Circuit-Digest/LiteWing/Documents/Images/Altitude-Change-Litewing.gif

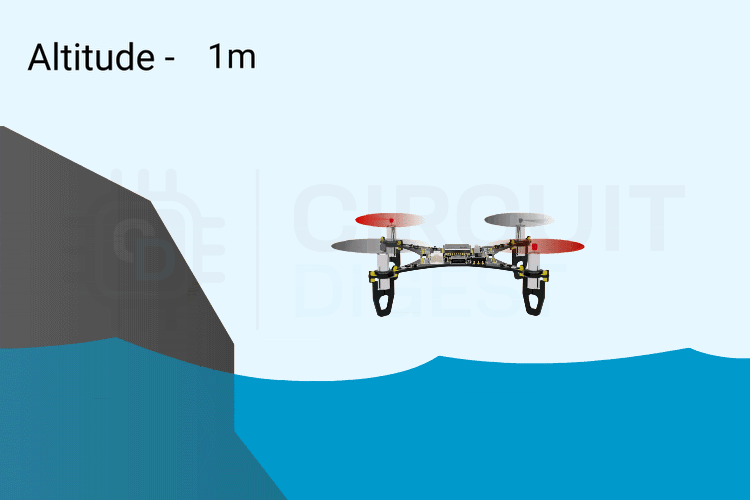
Documents/Images/Altitude-Change-Litewing.gif
