Circuit-Digest/LiteWing/Documents/Images/Calculated-height-displayed-GIF.gif

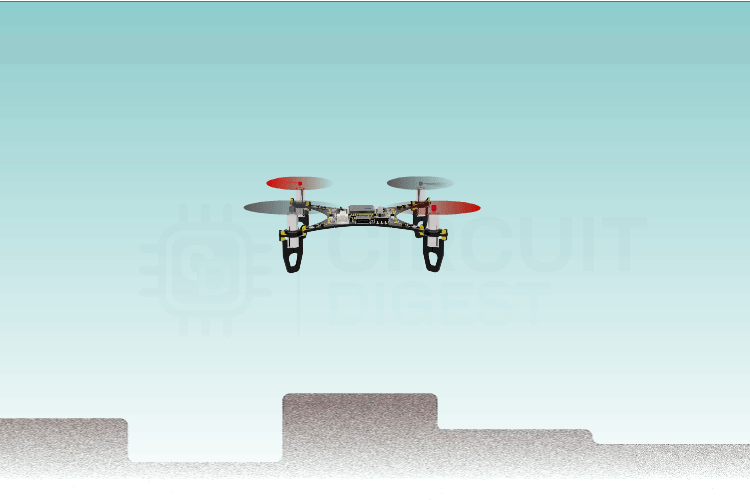
Documents/Images/Calculated-height-displayed-GIF.gif
