Circuit-Digest/LiteWing/Documents/Images/GIF-Ultrasonic-Wave-Height-Hold.gif

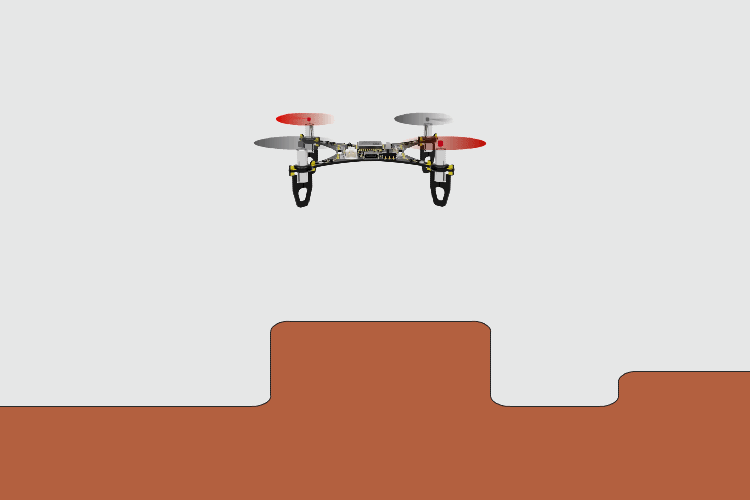
Documents/Images/GIF-Ultrasonic-Wave-Height-Hold.gif
