Circuit-Digest/LiteWing/Python-Scripts/crazyflie-clients-python/docs/images/base_station_geo_dialog.png

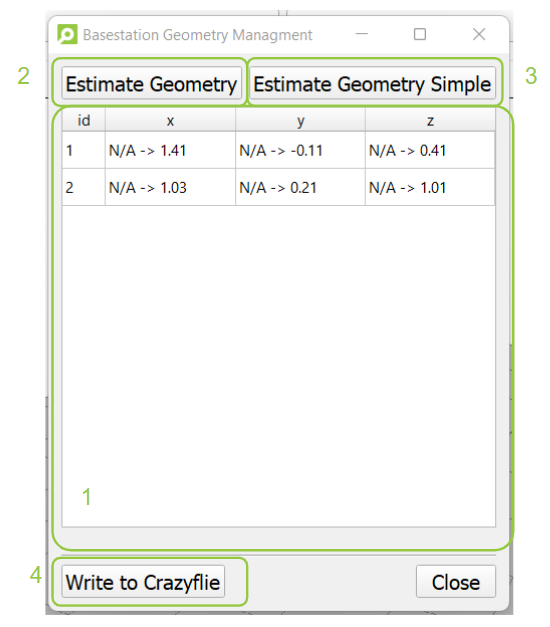
Python-Scripts/crazyflie-clients-python/docs/images/base_station_geo_dialog.png
