Circuit-Digest/LiteWing/Python-Scripts/crazyflie-clients-python/docs/images/bootloader-recovery.png

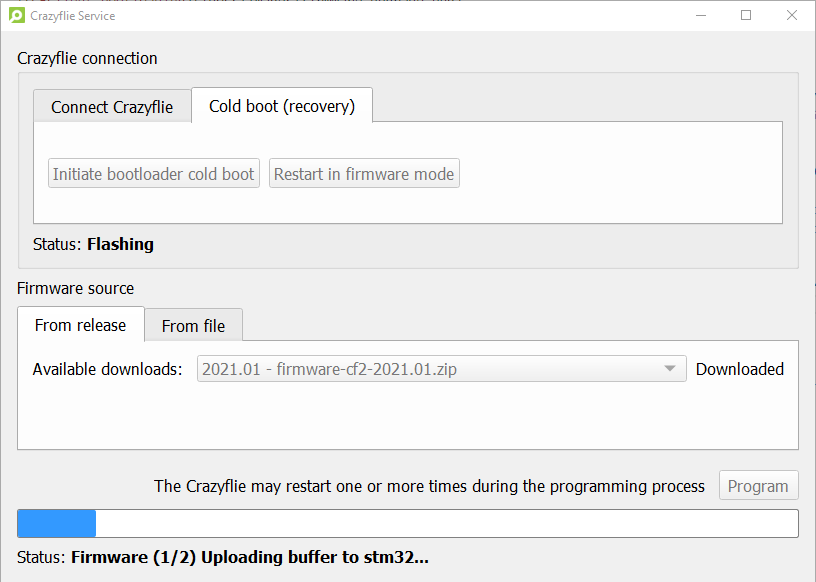
Python-Scripts/crazyflie-clients-python/docs/images/bootloader-recovery.png
