Circuit-Digest/LiteWing/Python-Scripts/crazyflie-clients-python/docs/images/cfclient_anchor_identification.png

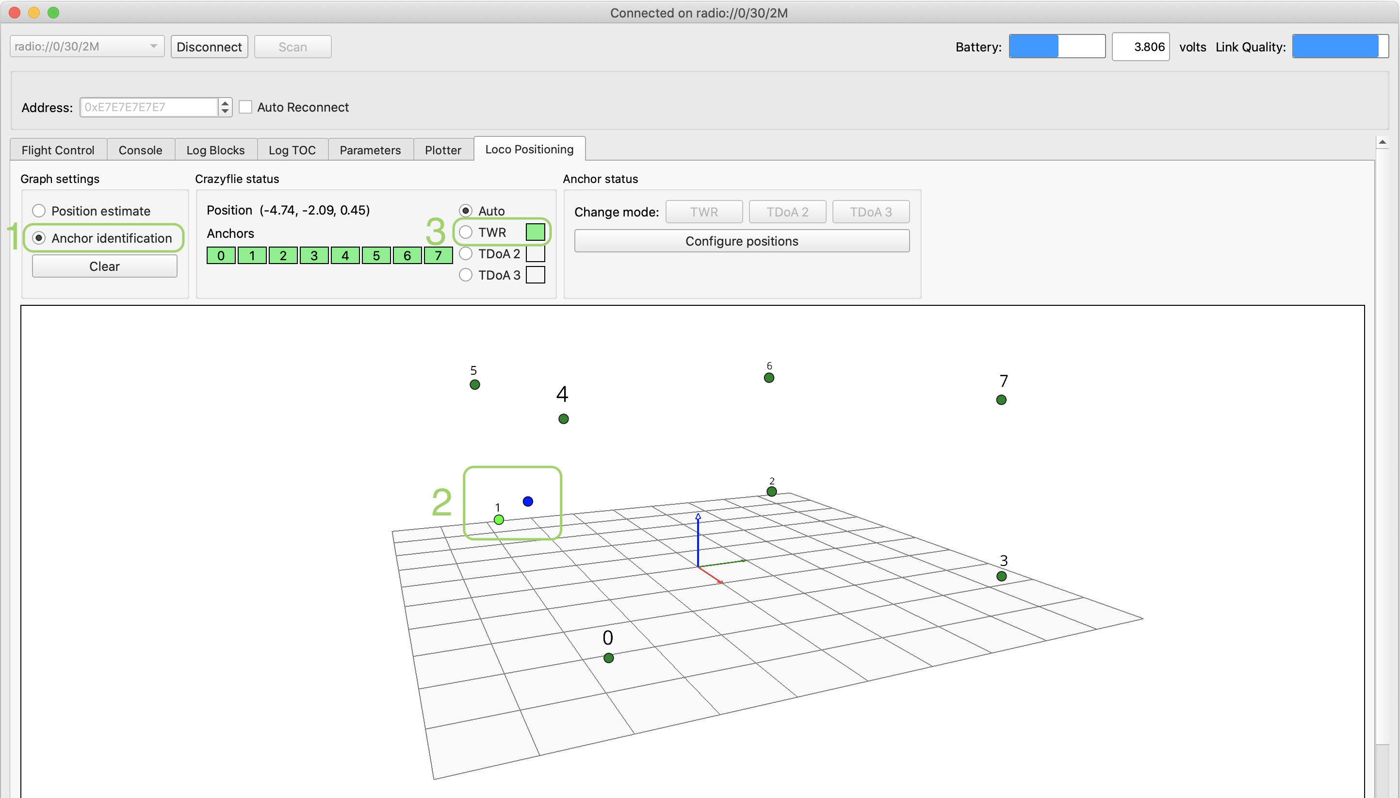
Python-Scripts/crazyflie-clients-python/docs/images/cfclient_anchor_identification.png
