Circuit-Digest/LiteWing/Python-Scripts/crazyflie-clients-python/docs/images/cfclient_connect_dialog.png

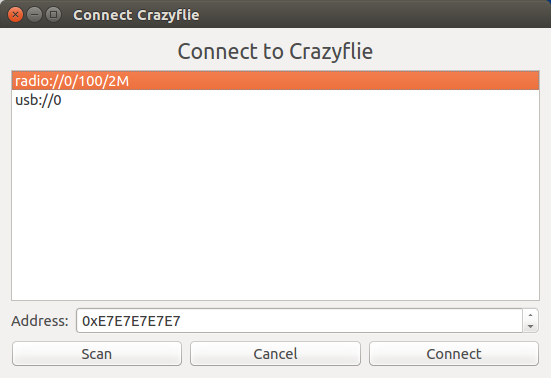
Python-Scripts/crazyflie-clients-python/docs/images/cfclient_connect_dialog.png
