Circuit-Digest/LiteWing/Python-Scripts/crazyflie-clients-python/docs/images/cfclient_connected.png

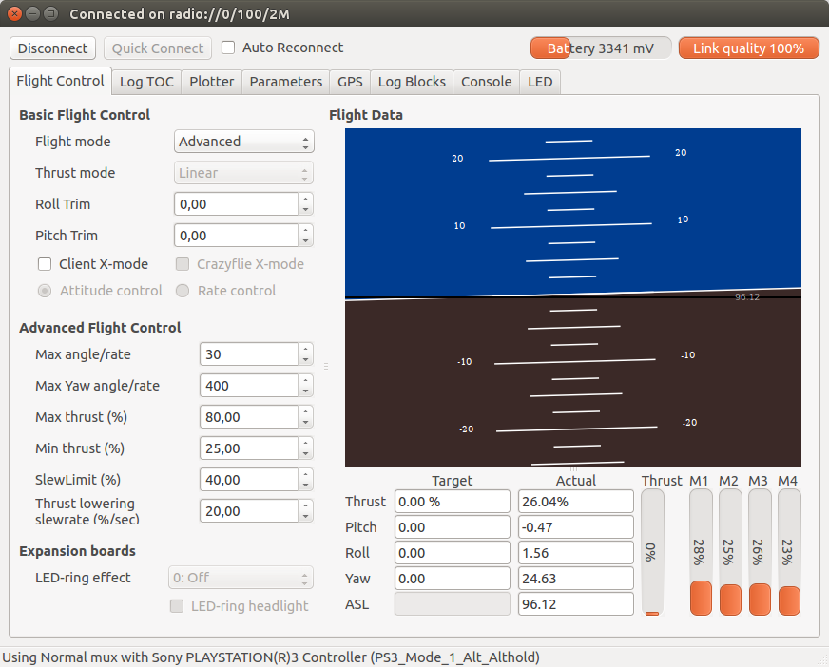
Python-Scripts/crazyflie-clients-python/docs/images/cfclient_connected.png
