Circuit-Digest/LiteWing/Python-Scripts/crazyflie-clients-python/docs/images/cfclient_console_marked.png

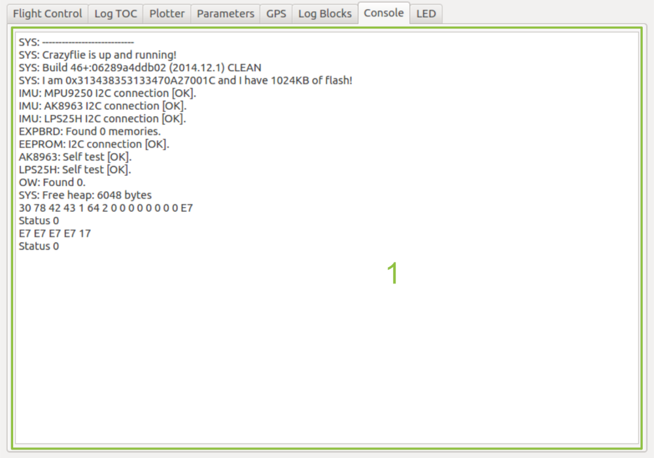
Python-Scripts/crazyflie-clients-python/docs/images/cfclient_console_marked.png
