Circuit-Digest/LiteWing/Python-Scripts/crazyflie-clients-python/docs/images/cfclient_frontpage.png

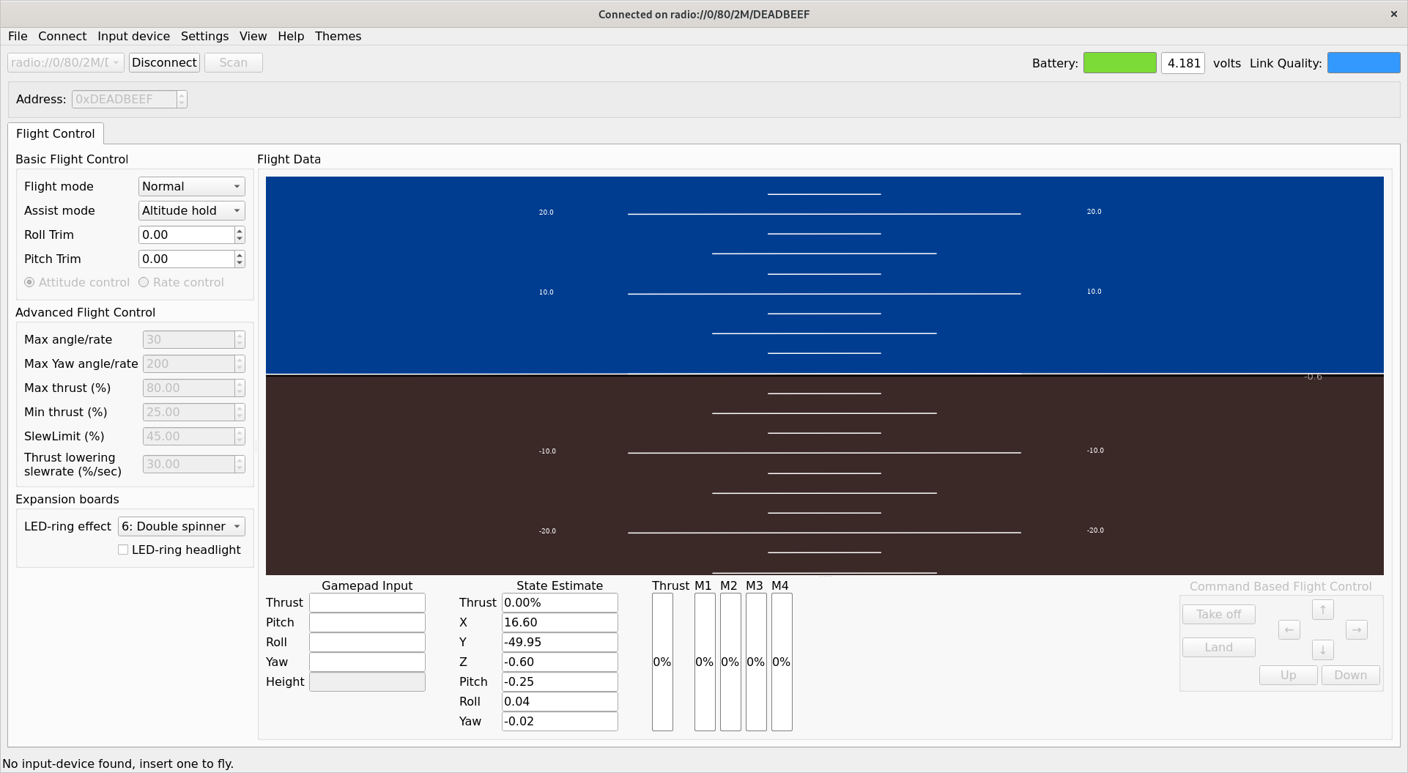
Python-Scripts/crazyflie-clients-python/docs/images/cfclient_frontpage.png
