Circuit-Digest/LiteWing/Python-Scripts/crazyflie-clients-python/docs/images/cfclient_input_student_device.png

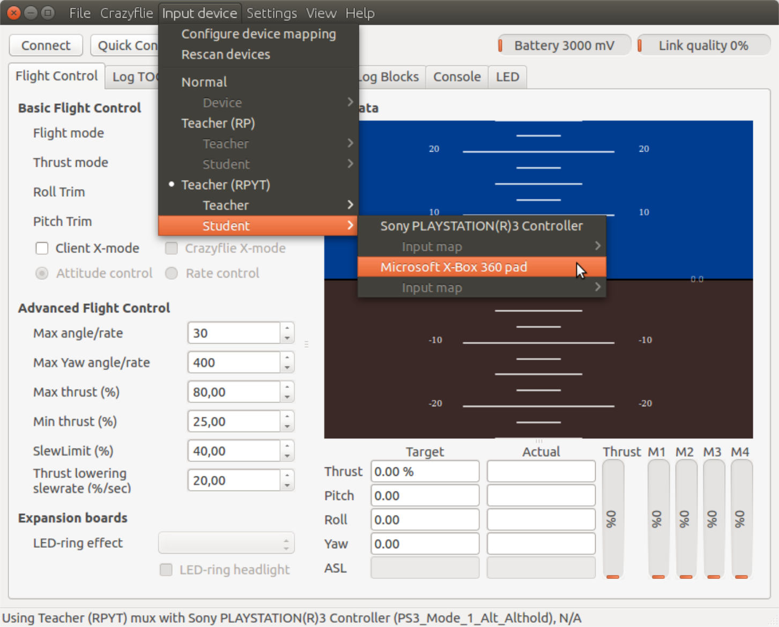
Python-Scripts/crazyflie-clients-python/docs/images/cfclient_input_student_device.png
