Circuit-Digest/LiteWing/Python-Scripts/crazyflie-clients-python/docs/images/cfclient_input_teacher_device.png

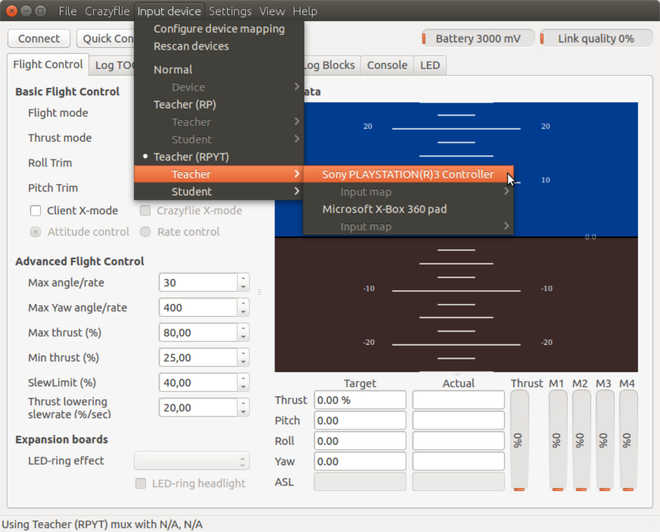
Python-Scripts/crazyflie-clients-python/docs/images/cfclient_input_teacher_device.png
