Circuit-Digest/LiteWing/Python-Scripts/crazyflie-clients-python/docs/images/cfclient_lh_main.png

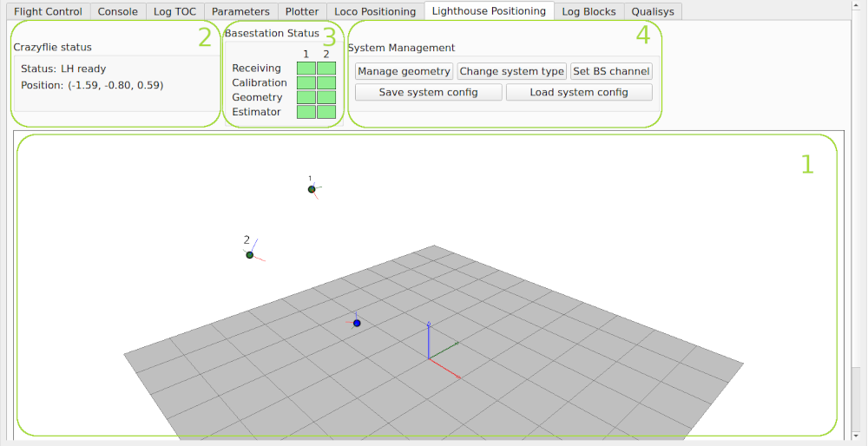
Python-Scripts/crazyflie-clients-python/docs/images/cfclient_lh_main.png
