Circuit-Digest/LiteWing/Python-Scripts/crazyflie-clients-python/docs/images/cfclient_param.png

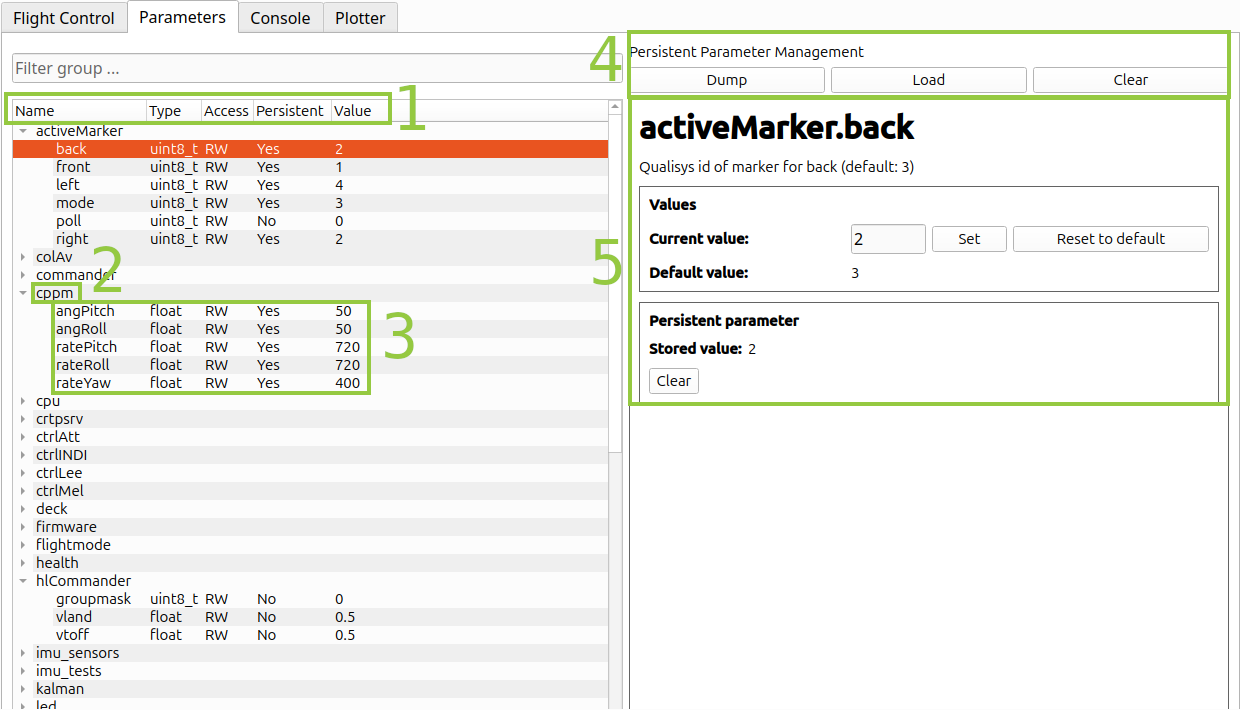
Python-Scripts/crazyflie-clients-python/docs/images/cfclient_param.png
