Circuit-Digest/LiteWing/Python-Scripts/crazyflie-clients-python/docs/images/cfclient_plotter.png

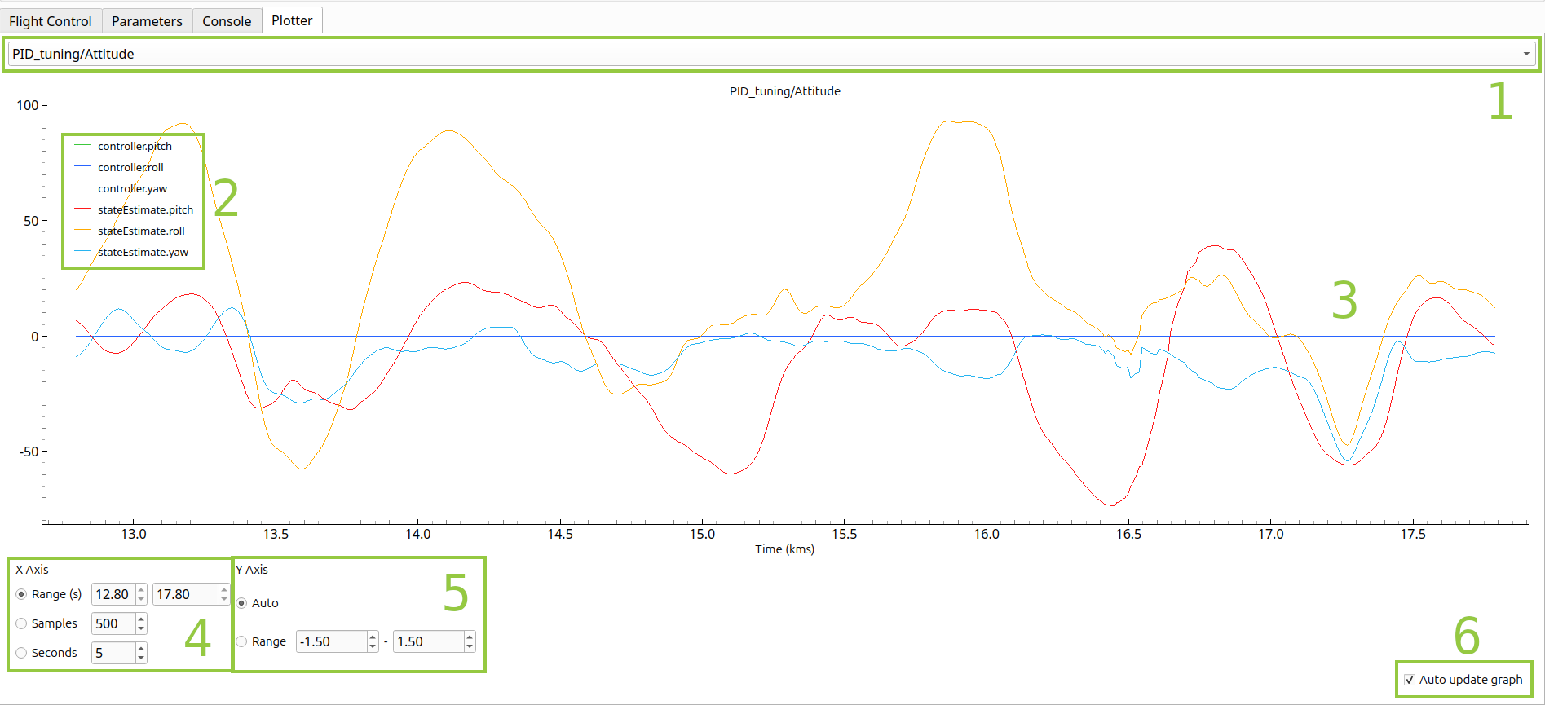
Python-Scripts/crazyflie-clients-python/docs/images/cfclient_plotter.png
