Circuit-Digest/LiteWing/Python-Scripts/crazyflie-clients-python/docs/images/configure_cf1.png

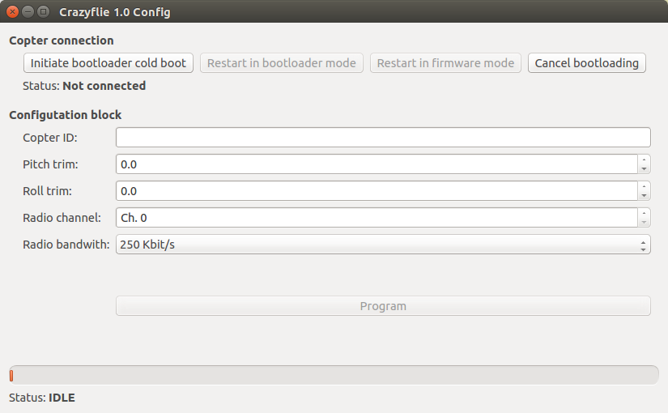
Python-Scripts/crazyflie-clients-python/docs/images/configure_cf1.png
