Circuit-Digest/LiteWing/Python-Scripts/crazyflie-clients-python/docs/images/image00.png

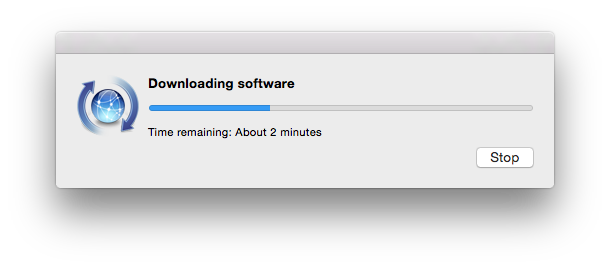
Python-Scripts/crazyflie-clients-python/docs/images/image00.png
