Circuit-Digest/LiteWing/Python-Scripts/crazyflie-clients-python/docs/images/image01.png

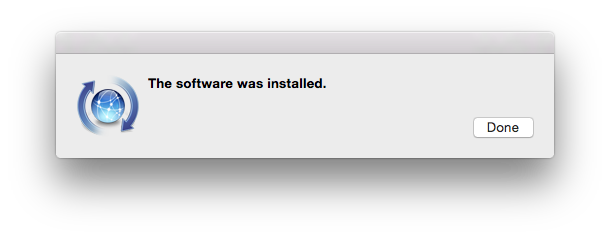
Python-Scripts/crazyflie-clients-python/docs/images/image01.png
