Circuit-Digest/LiteWing/Python-Scripts/crazyflie-clients-python/docs/images/image02.png

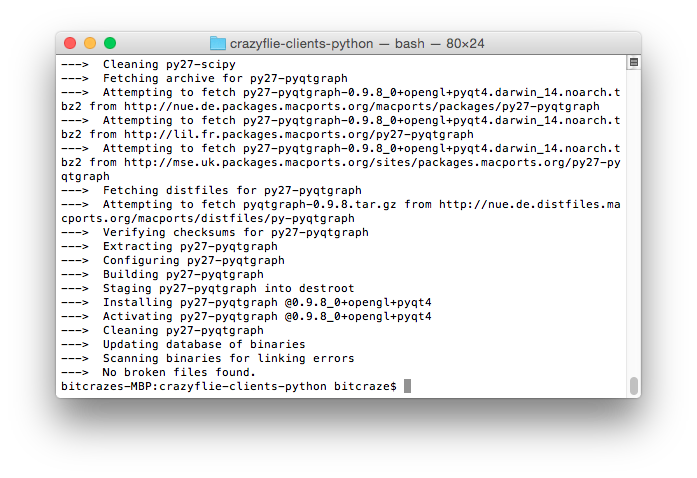
Python-Scripts/crazyflie-clients-python/docs/images/image02.png
