Circuit-Digest/LiteWing/Python-Scripts/crazyflie-clients-python/docs/images/image03.png

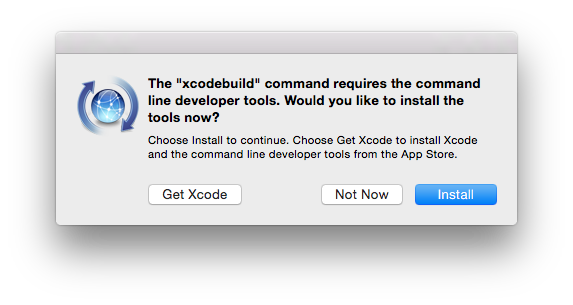
Python-Scripts/crazyflie-clients-python/docs/images/image03.png
