Circuit-Digest/LiteWing/Python-Scripts/crazyflie-clients-python/docs/images/image04.png

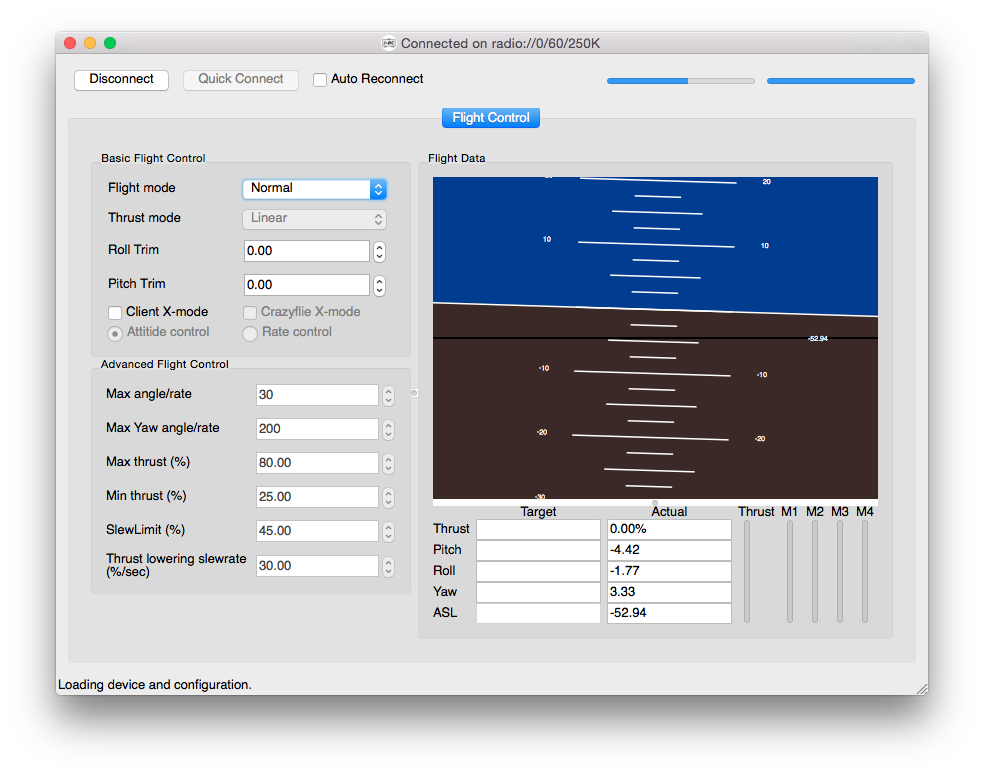
Python-Scripts/crazyflie-clients-python/docs/images/image04.png
