Circuit-Digest/LiteWing/Python-Scripts/crazyflie-clients-python/docs/images/image05.png

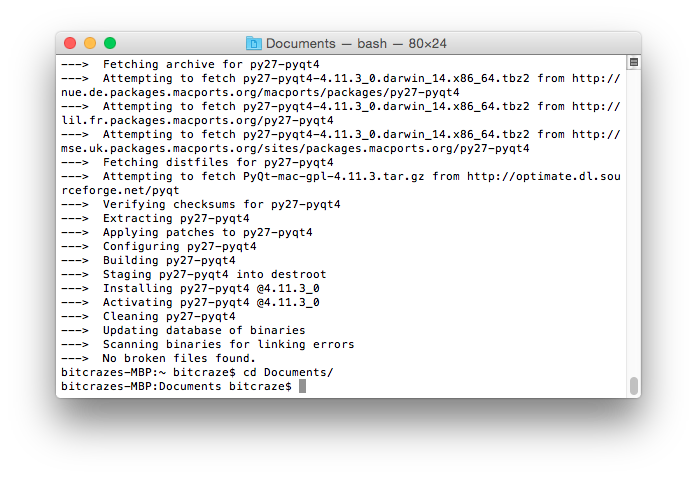
Python-Scripts/crazyflie-clients-python/docs/images/image05.png
