Circuit-Digest/LiteWing/Python-Scripts/crazyflie-clients-python/docs/images/image06.png

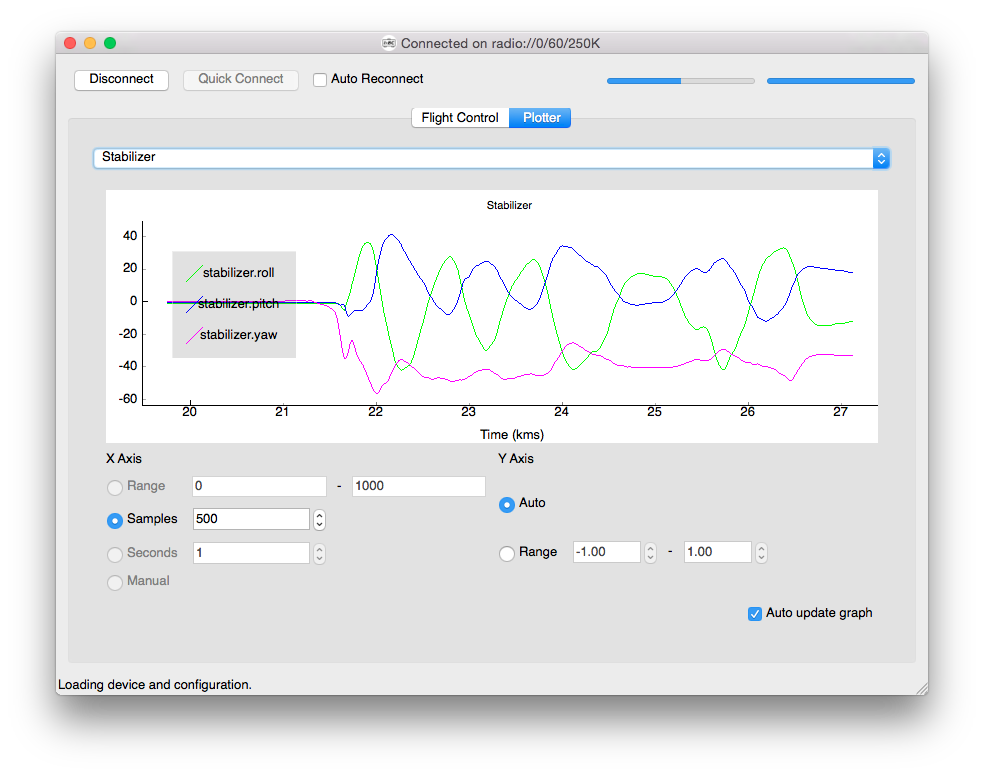
Python-Scripts/crazyflie-clients-python/docs/images/image06.png
