Circuit-Digest/LiteWing/Python-Scripts/crazyflie-clients-python/docs/images/tuning_tab.png

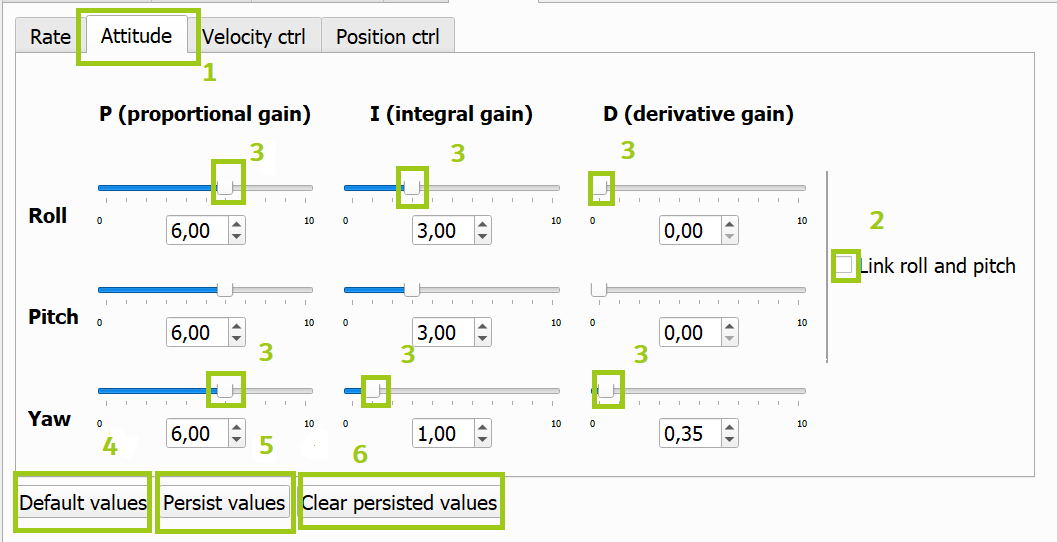
Python-Scripts/crazyflie-clients-python/docs/images/tuning_tab.png
