Circuit-Digest/LiteWing/Python-Scripts/crazyflie-clients-python/src/cfclient/gui.py

# -*- coding: utf-8 -*-
#
#     ||          ____  _ __
#  +------+      / __ )(_) /_______________ _____  ___
#  | 0xBC |     / __  / / __/ ___/ ___/ __ `/_  / / _ \
#  +------+    / /_/ / / /_/ /__/ /  / /_/ / / /_/  __/
#   ||  ||    /_____/_/\__/\___/_/   \__,_/ /___/\___/
#
#  Copyright (C) 2011-2023 Bitcraze AB
#
#  Crazyflie Nano Quadcopter Client
#
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
"""Initialization of the PC Client GUI."""

import platform
import sys
import os
import argparse
import datetime
import signal

import logging

import cfclient

__author__ = 'Bitcraze AB'
__all__ = []


def handle_sigint(app):
    logging.info('SIGINT received, exiting ...')
    if app:
        app.closeAllWindows()
    else:
        sys.exit(0)


def main():
    """
    Check starting conditions and start GUI.

    First, check command line arguments and start loggers. Set log levels. Try
    all imports and exit verbosely if a library is not found. Disable outputs
    to stdout and start the GUI.
    """
    app = None

    # Connect ctrl-c (SIGINT) signal
    signal.signal(signal.SIGINT, lambda sig, frame: handle_sigint(app))

    # Allows frozen mac build to load libraries from app bundle
    if getattr(sys, 'frozen', False) and platform.system() == 'Darwin':
        os.environ['DYLD_FALLBACK_LIBRARY_PATH'] = os.path.dirname(
            sys.executable)

    # Set ERROR level for PyQt logger
    qtlogger = logging.getLogger('PyQt6')
    qtlogger.setLevel(logging.ERROR)

    parser = argparse.ArgumentParser(
        description="cfclient - Crazyflie graphical control client")
    parser.add_argument('--debug', '-d', nargs=1, default='info', type=str,
                        help="set debug level "
                             "[minimal, info, debug, debugfile]")
    parser.add_argument('--check-imports', type=bool, default=False,
                        const=True, nargs="?",
                        help="Check python imports and exit successfully" +
                        " (intended for CI)")
    args = parser.parse_args()
    debug = args.debug

    cflogger = logging.getLogger('')

    # Set correct logging fuctionality according to commandline
    if ("debugfile" in debug):
        logging.basicConfig(level=logging.DEBUG)
        # Add extra format options for file logger (thread and time)
        formatter = logging.Formatter('%(asctime)s:%(threadName)s:%(name)'
                                      's:%(levelname)s:%(message)s')
        filename = "debug-%s.log" % datetime.datetime.now()
        filehandler = logging.FileHandler(filename)
        filehandler.setLevel(logging.DEBUG)
        filehandler.setFormatter(formatter)
        cflogger.addHandler(filehandler)
    elif ("debug" in debug):
        logging.basicConfig(level=logging.DEBUG)
    elif ("minimal" in debug):
        logging.basicConfig(level=logging.WARNING)
    elif ("info" in debug):
        logging.basicConfig(level=logging.INFO)

    logger = logging.getLogger(__name__)

    logger.debug("Using config path {}".format(cfclient.config_path))
    logger.debug("sys.path={}".format(sys.path))

    # Try all the imports used in the project here to control what happens....
    try:
        import usb  # noqa
    except ImportError:
        logger.critical("No pyusb installation found, exiting!")
        sys.exit(1)

    if not sys.platform.startswith('linux'):
        try:
            import sdl2  # noqa
        except ImportError:
            logger.critical("No pysdl2 installation found, exiting!")
            sys.exit(1)

    try:
        import PyQt6  # noqa
    except ImportError:
        logger.critical("No PyQT6 installation found, exiting!")
        sys.exit(1)

    # Disable printouts from STL
    if os.name == 'posix':
        stdout = os.dup(1)
        os.dup2(os.open('/dev/null', os.O_WRONLY), 1)
        sys.stdout = os.fdopen(stdout, 'w')
        logger.info("Disabling STL printouts")

    if os.name == 'nt':
        stdout = os.dup(1)
        os.dup2(os.open('NUL', os.O_WRONLY), 1)
        sys.stdout = os.fdopen(stdout, 'w')
        logger.info("Disabling STL printouts")

    if sys.platform == 'darwin':
        try:
            import Foundation
            bundle = Foundation.NSBundle.mainBundle()
            if bundle:
                info = (bundle.localizedInfoDictionary() or
                        bundle.infoDictionary())
                if info:
                    info['CFBundleName'] = 'Crazyflie'
        except ImportError:
            logger.info("Foundation not found. Menu will show python as "
                        "application name")

    if args.check_imports:
        logger.info("All imports successful!")
        sys.exit(0)

    # Start up the main user-interface
    from .ui.main import MainUI
    from PyQt6.QtWidgets import QApplication
    from PyQt6.QtGui import QIcon

    if os.name == 'posix':
        logger.info('If startup fails because of "xcb", install dependency with `sudo apt install libxcb-xinerama0`.')

    app = QApplication(sys.argv)
    app.setStyle("Fusion")
    from cfclient.utils.ui import UiUtils

    app.setWindowIcon(QIcon(cfclient.module_path + "/ui/icons/icon-256.png"))
    app.setApplicationName("Crazyflie client")
    # Make sure the right icon is set in Windows 7+ taskbar
    if os.name == 'nt':
        import ctypes

        try:
            myappid = 'mycompany.myproduct.subproduct.version'
            ctypes.windll.shell32.SetCurrentProcessExplicitAppUserModelID(
                myappid)
        except Exception:
            pass

    main_window = MainUI()
    app.setFont(UiUtils.FONT)
    main_window.show()
    main_window.set_default_theme()
    sys.exit(app.exec())


if __name__ == "__main__":
    main()
